omenmicro/bravo/hw/bravo-issue3.png

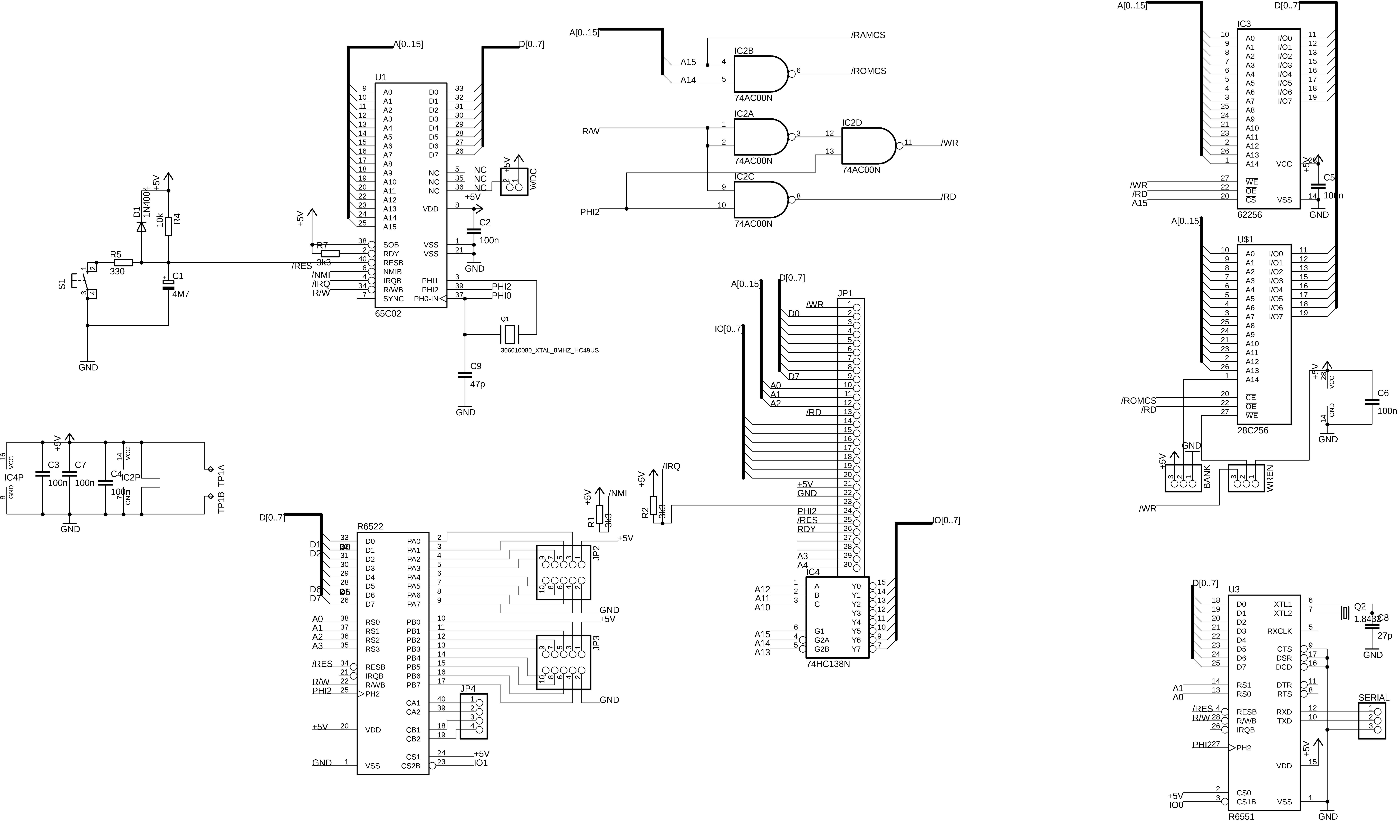
hw/bravo-issue3.png
